StefanHermannBerlin/HASSIO-EasyPrototyping/img/hassio-reboot.gif

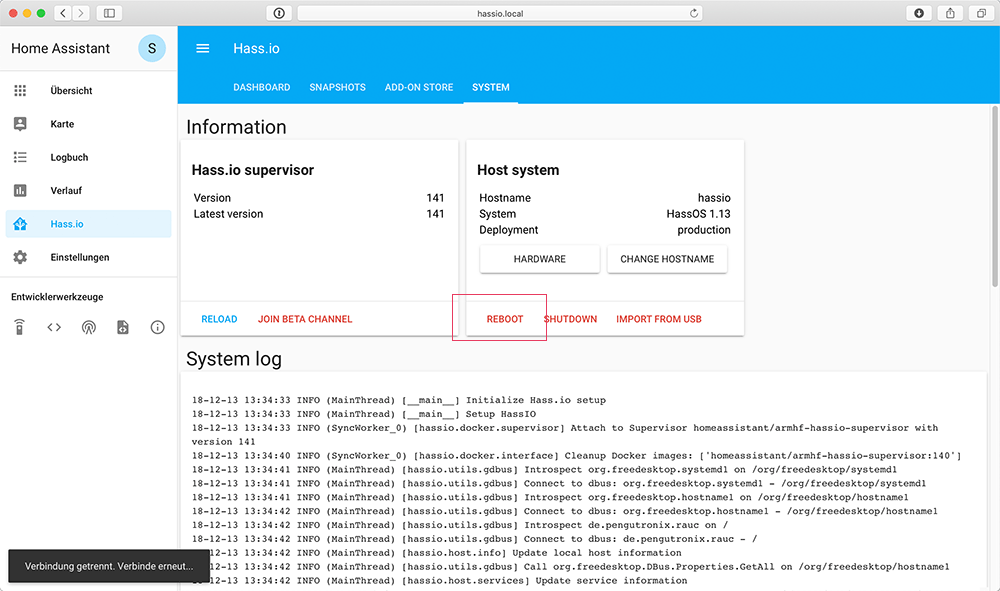
img/hassio-reboot.gif
