StefanHermannBerlin/HASSIO-EasyPrototyping/img/hassio_configurator_backend_integration.jpg

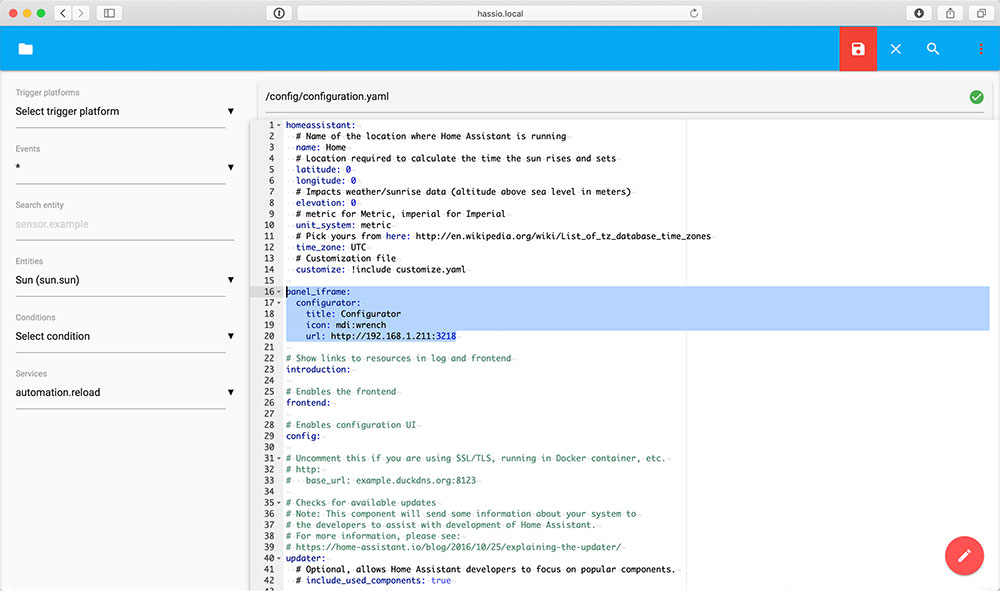
img/hassio_configurator_backend_integration.jpg
