StefanHermannBerlin/HASSIO-EasyPrototyping/img/hassio_configurator_config.gif

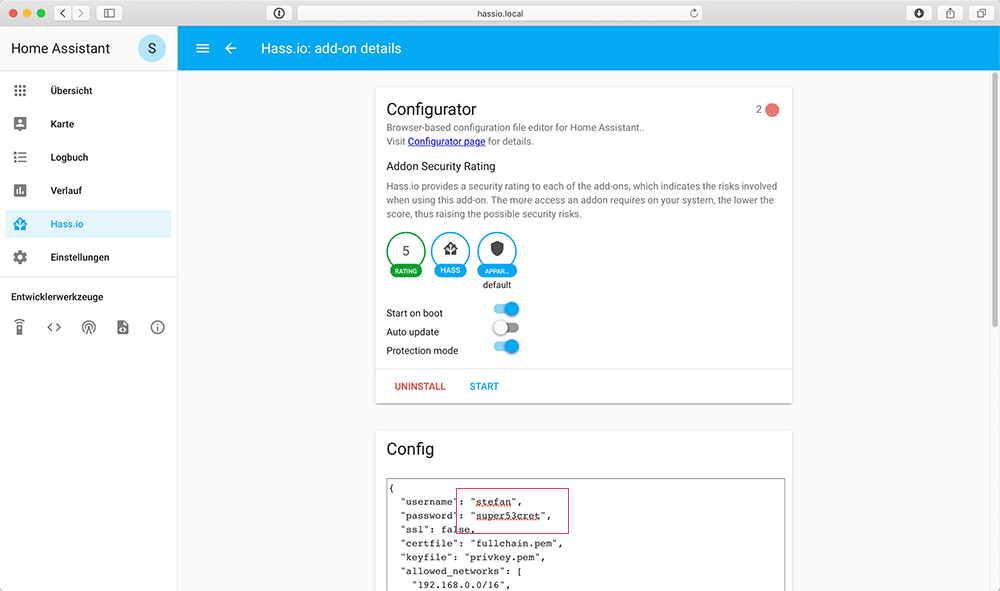
img/hassio_configurator_config.gif
