StefanHermannBerlin/HASSIO-EasyPrototyping/img/hassio_enable_mqtt.gif

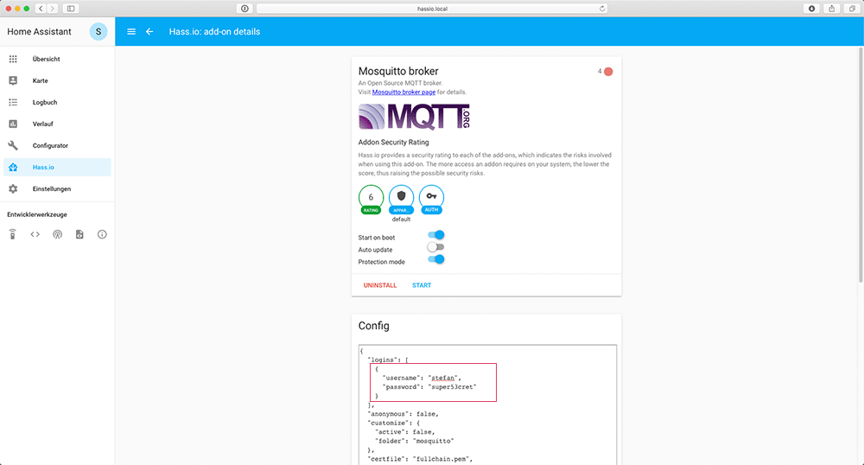
img/hassio_enable_mqtt.gif
