StefanHermannBerlin/HASSIO-EasyPrototyping/img/hassio_firstscreen.png

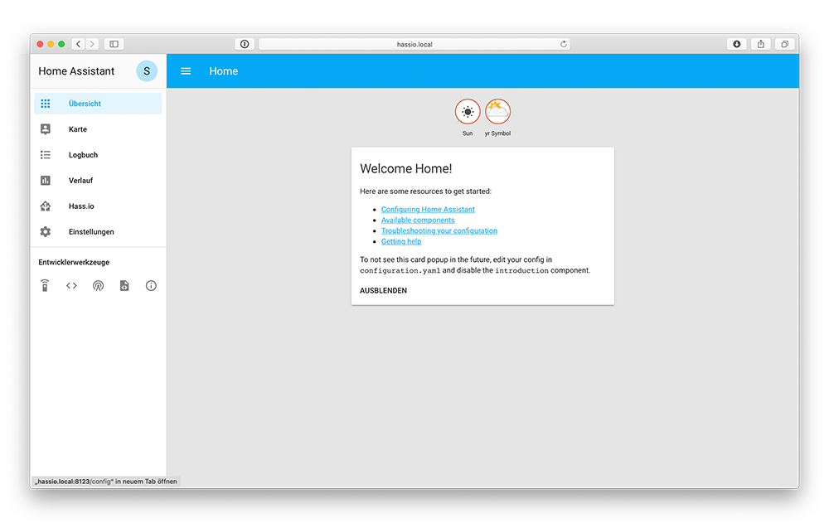
img/hassio_firstscreen.png
