StefanHermannBerlin/HASSIO-EasyPrototyping/img/hassio_new_devices.gif

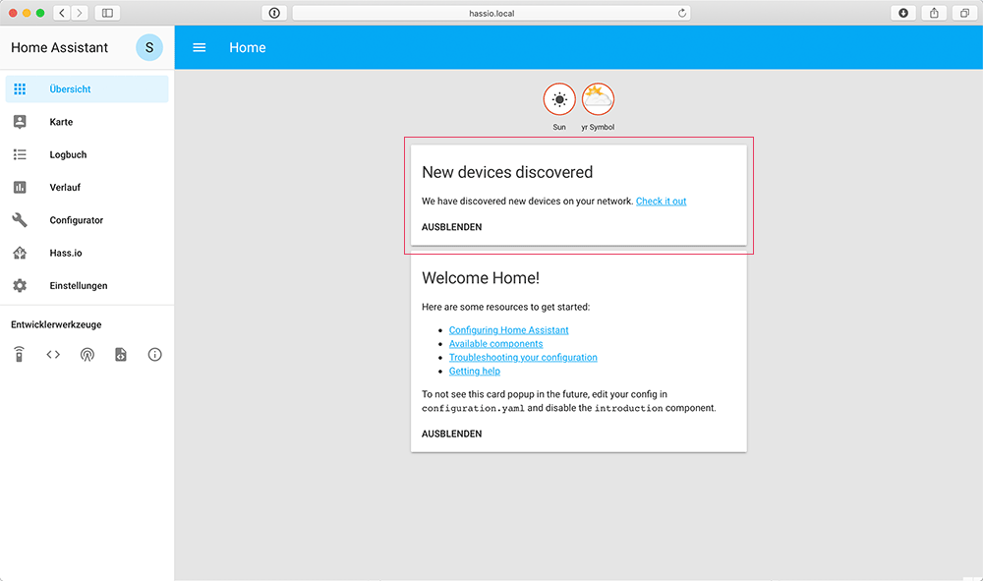
img/hassio_new_devices.gif
