StefanHermannBerlin/HASSIO-EasyPrototyping/img/ssh-terminal.gif

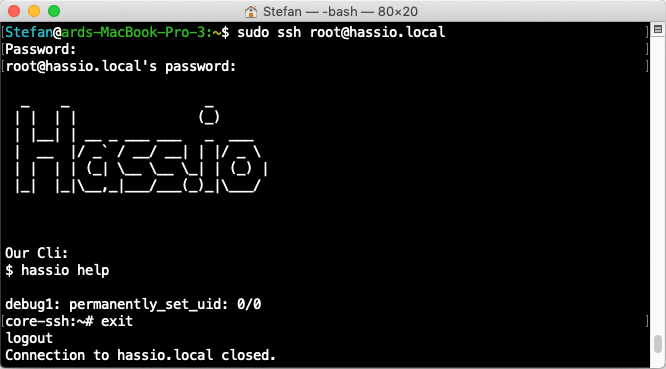
img/ssh-terminal.gif
