StefanHermannBerlin/HASSIO-EasyPrototyping/img/hassio_configurator_installation.gif

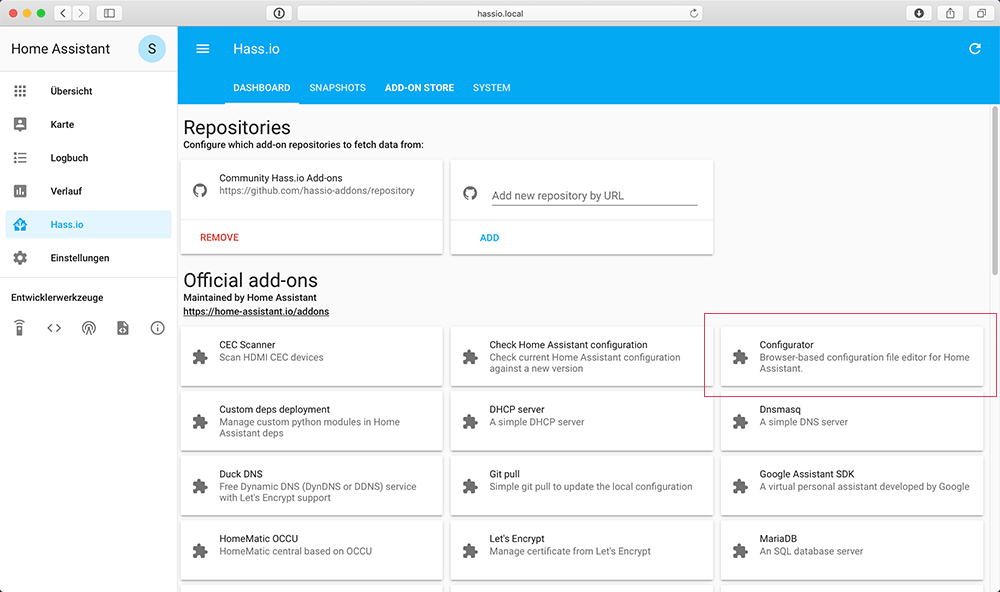
img/hassio_configurator_installation.gif
