StefanHermannBerlin/HASSIO-EasyPrototyping/img/step1-setup.gif

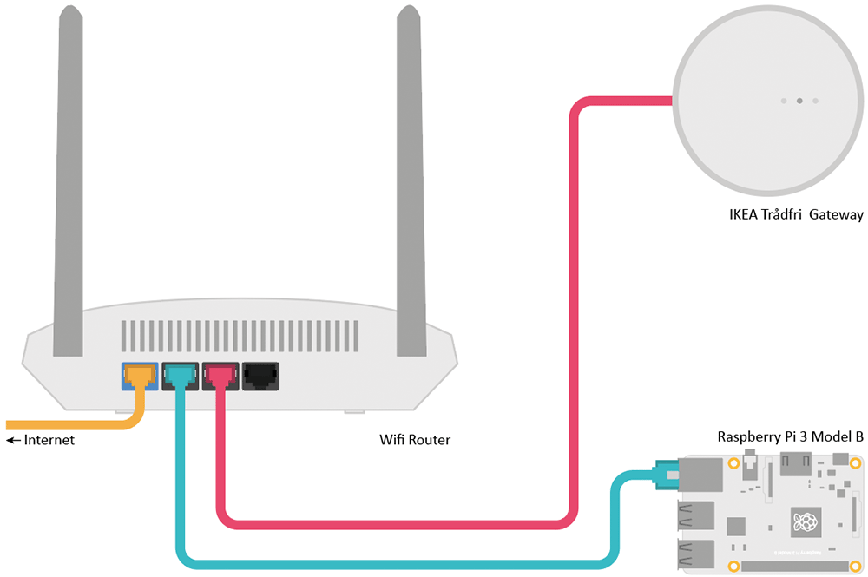
img/step1-setup.gif
